IGS1I/Hydroponic-Automation-System/HardwareSchematics/HardwareSchematics.kicad_sch

## KiCad design HardwareSchematics/HardwareSchematics.kicad_sch (2025-12-16)

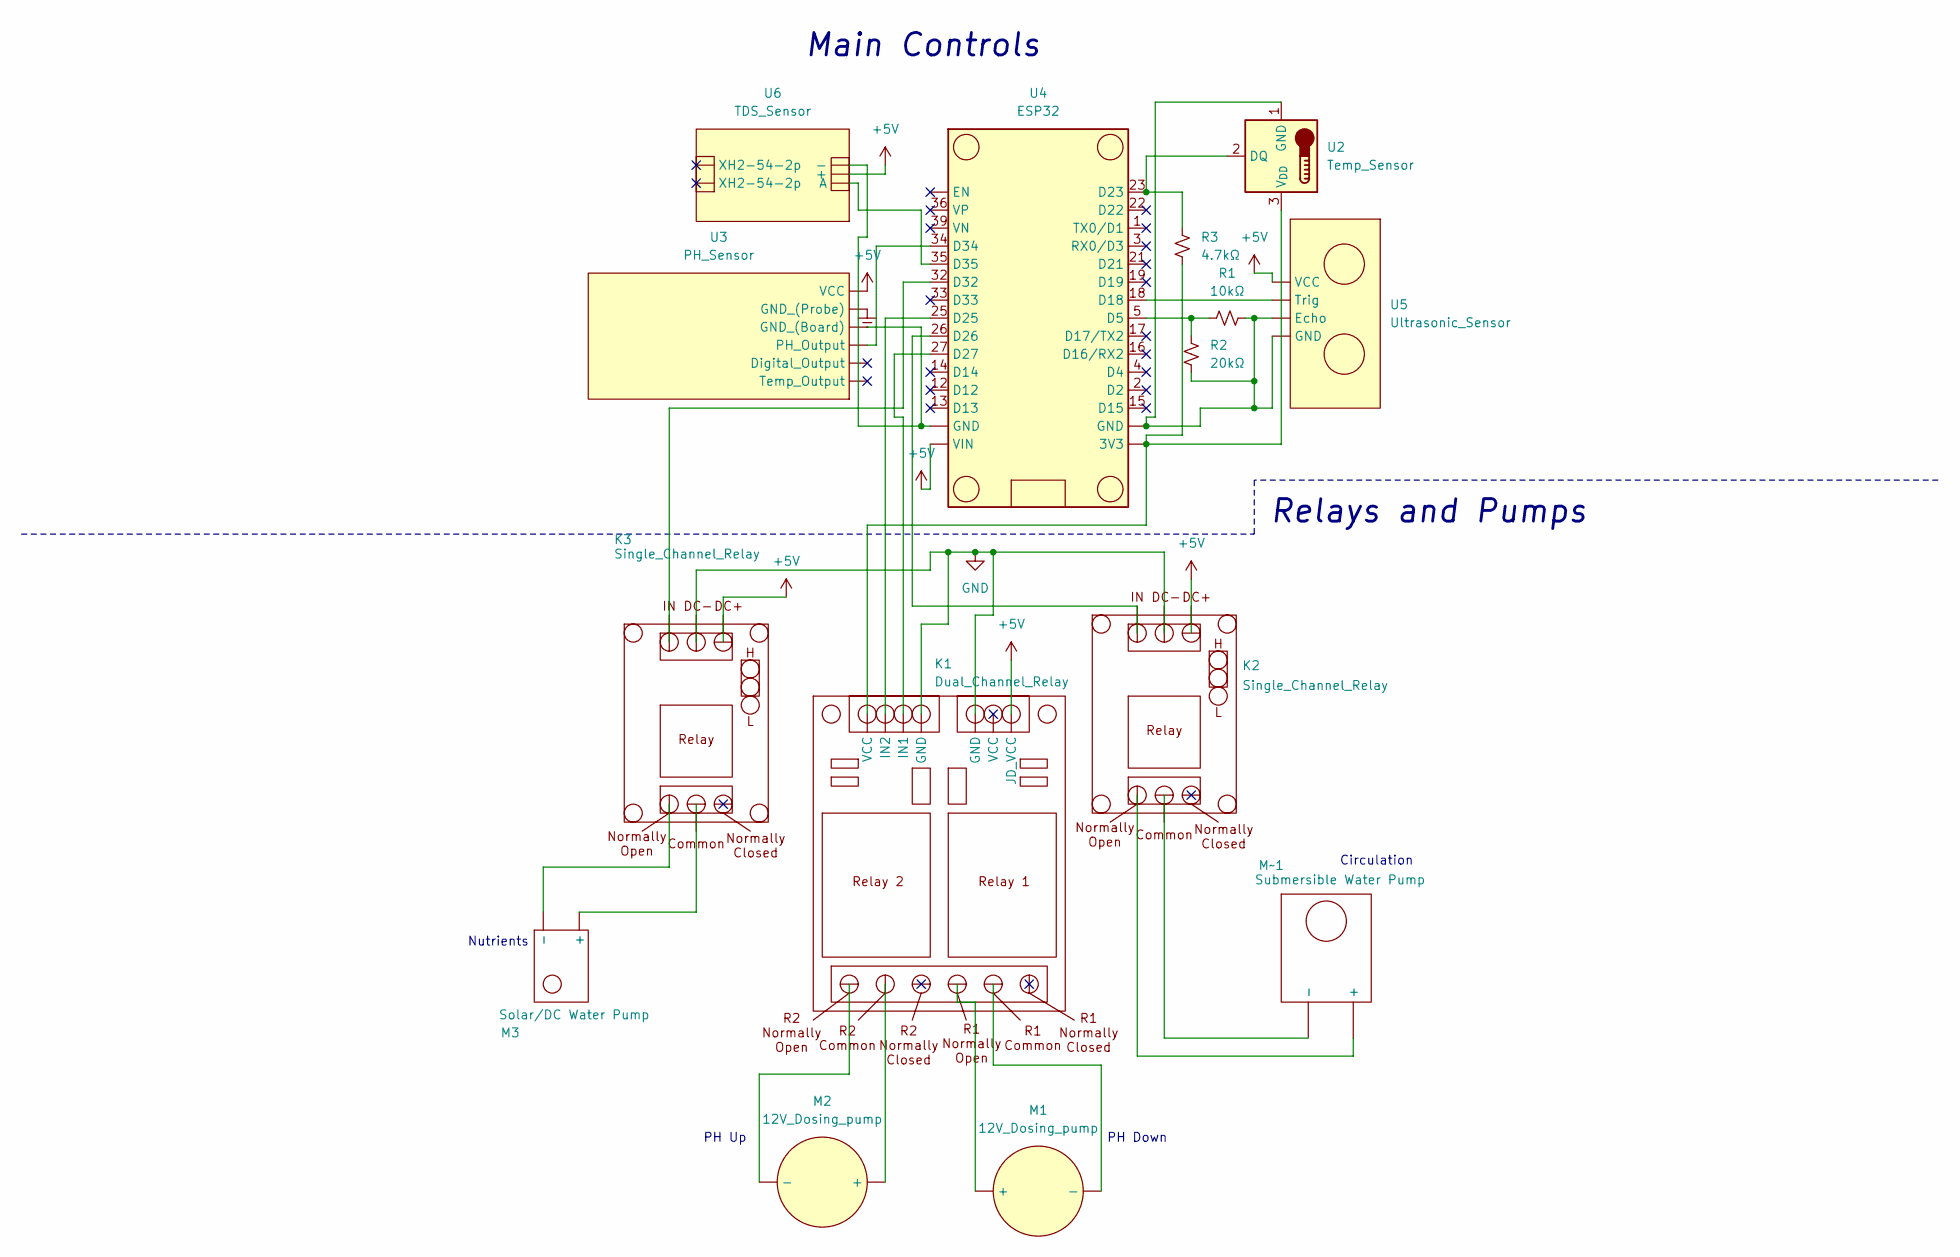
[picture p18: schematic HardwareSchematics.kicad_sch]

Parts:
K1: Dual_Channel_Relay
K2, K3: Single_Channel_Relay
M1, M2: 12V_Dosing_pump
M3: Solar/DC Water Pump
M~1: Submersible Water Pump
R1: 10kΩ
R2: 20kΩ
R3: 4.7kΩ
U2: Temp_Sensor; TO-92_Inline
U3: PH_Sensor
U4: ESP32
U5: Ultrasonic_Sensor
U6: TDS_Sensor

Connections:
+5V: K1., K2., K3., U3., U4. (EN), U5., U6.
GND: K1., K2., K3.
unnamed: K1., M1., M2., R3.1, U2.3 (V_{DD}), U4. (EN), U4.25 (D25), U4.27 (D27)
unnamed: K2., M~1., U4.26 (D26)
unnamed: K3., M3., U4.32 (D32)
unnamed: R1.1, R2.1, U2.1 (GND), U4. (EN), U5.
unnamed: R1.2, R2.2, U4.5 (D5)
unnamed: R3.2, U2.2 (DQ), U4.23 (D23)
unnamed: U3., U4. (EN), U4.34 (D34), U6.
unnamed: U4.18 (D18), U5.
unnamed: U4.35 (D35), U6.
~: U3.

Notes on the sheet:
Nutrients
Main Controls
Circulation
PH Up
Relays and Pumps
PH Down
